MHI-Design/MaverickSpace-RaidEye/Donanım Tasarımı/3d_01.png

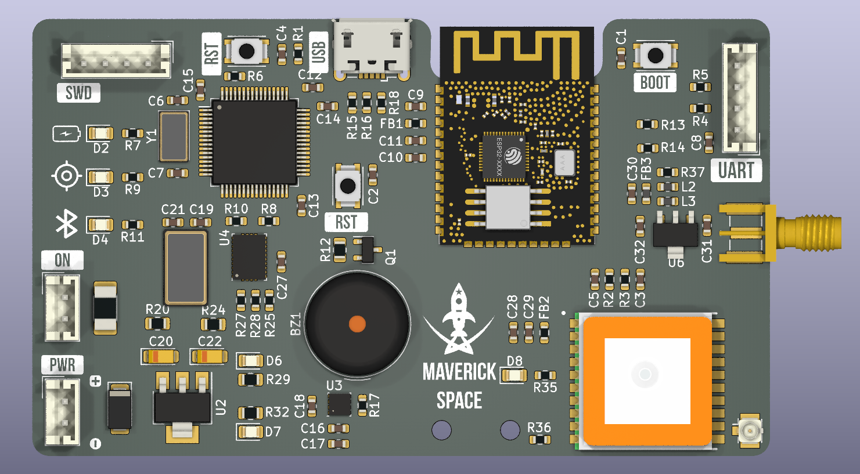
Donanım Tasarımı/3d_01.png
