MHI-Design/MaverickSpace-RaidEye/Donanım Tasarımı/animasyon_gorsel1.jpg

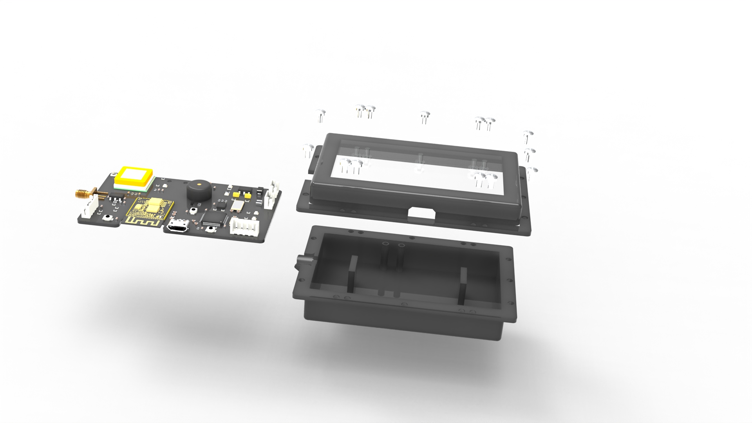
Donanım Tasarımı/animasyon_gorsel1.jpg
