MHI-Design/MaverickSpace-RaidEye/Mobil Uygulama Yazılımı/ana_sayfa.jpg

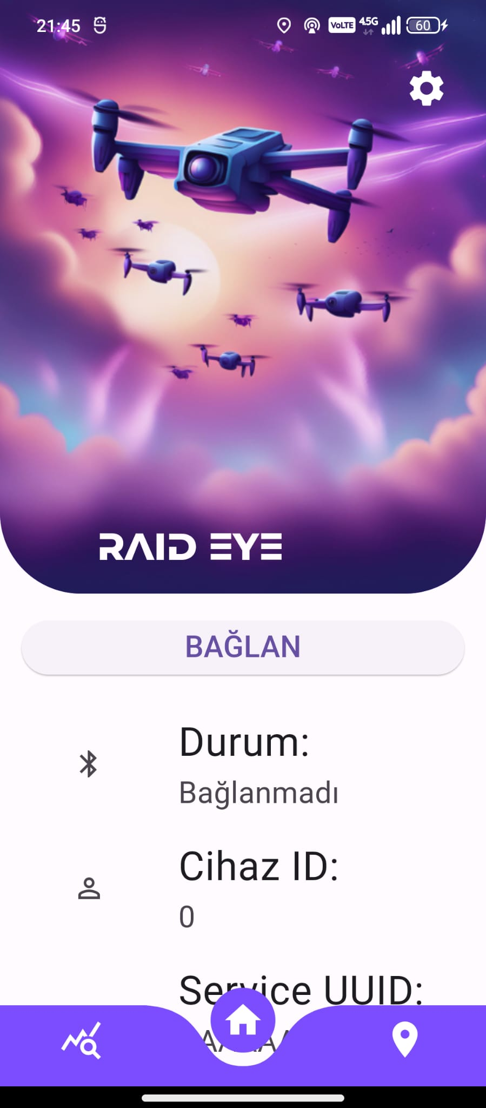
Mobil Uygulama Yazılımı/ana_sayfa.jpg
