MHI-Design/MaverickSpace-RaidEye/Mobil Uygulama Yazılımı/harita_sayfası_1.jpg

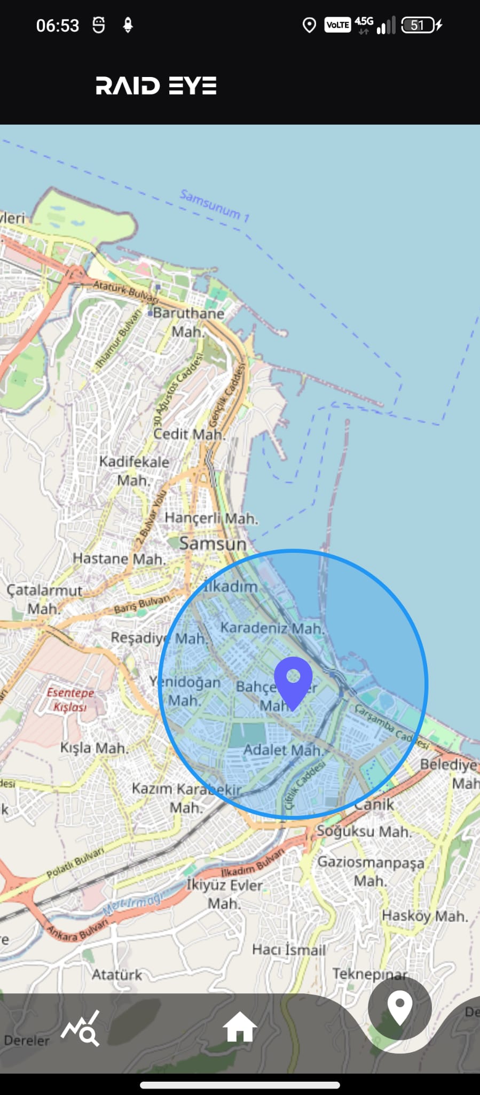
Mobil Uygulama Yazılımı/harita_sayfası_1.jpg
