MHI-Design/MaverickSpace-RaidEye/Mobil Uygulama Yazılımı/harita_sayfası_2.jpg

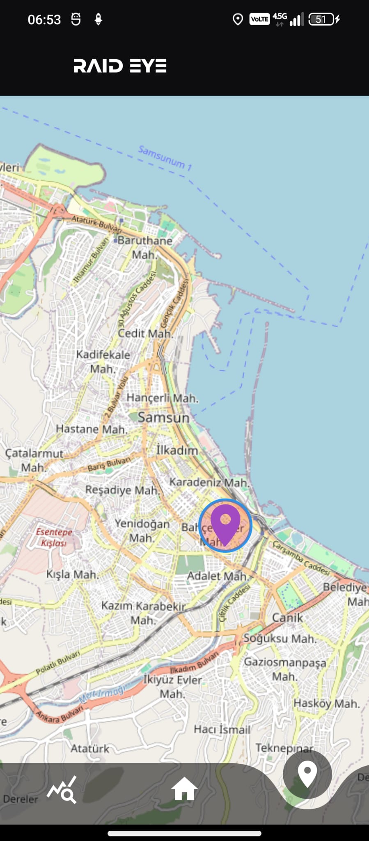
Mobil Uygulama Yazılımı/harita_sayfası_2.jpg
