MHI-Design/MaverickSpace-RaidEye/Mobil Uygulama Yazılımı/tablo_sayfası.jpg

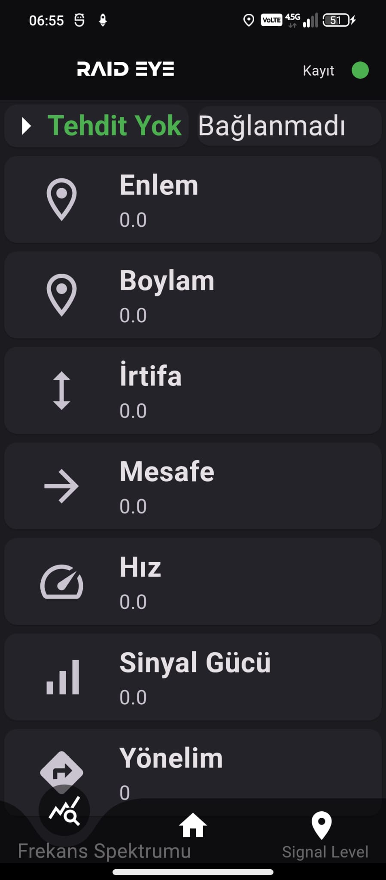
Mobil Uygulama Yazılımı/tablo_sayfası.jpg
